adbik4/DL-FinalProject/Images/DL_PCB_preview1.png

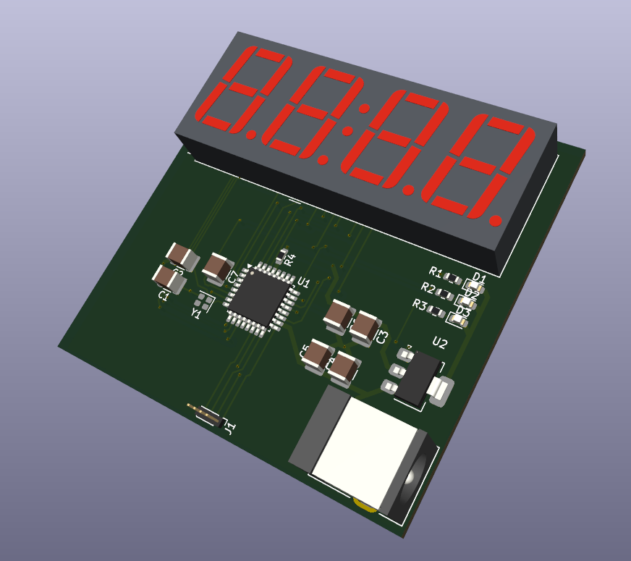
Images/DL_PCB_preview1.png
