adbik4/DL-FinalProject/Images/DL_PCB_state1.png

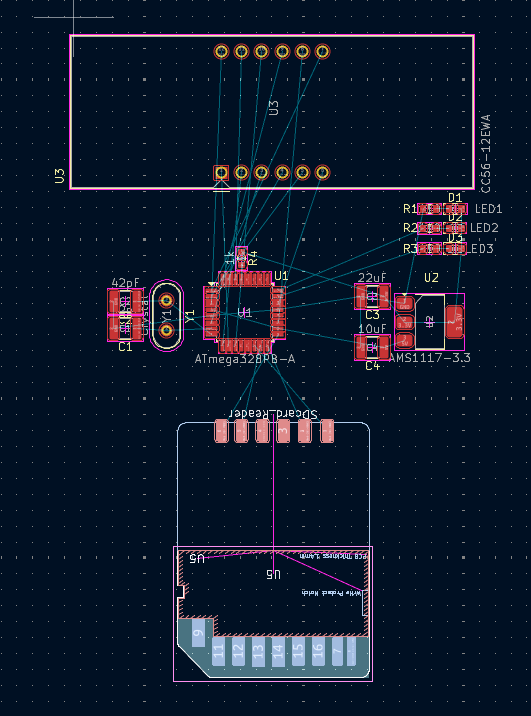
Images/DL_PCB_state1.png
