adbik4/DL-FinalProject/Images/DL_PCB_state3.png

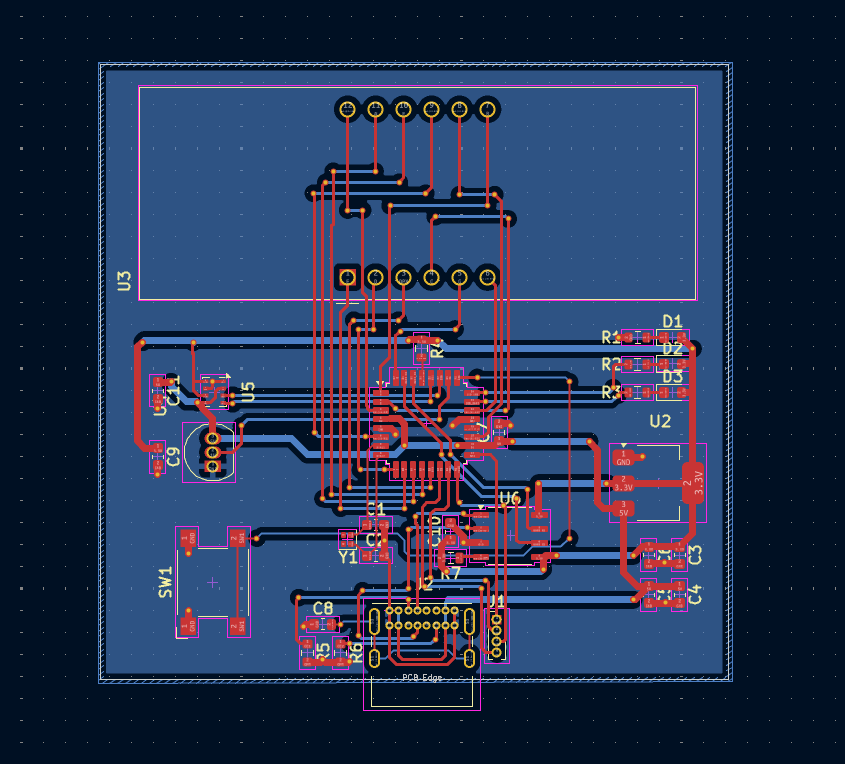
Images/DL_PCB_state3.png
