adbik4/DL-FinalProject/Images/DL_PCB_state4.png

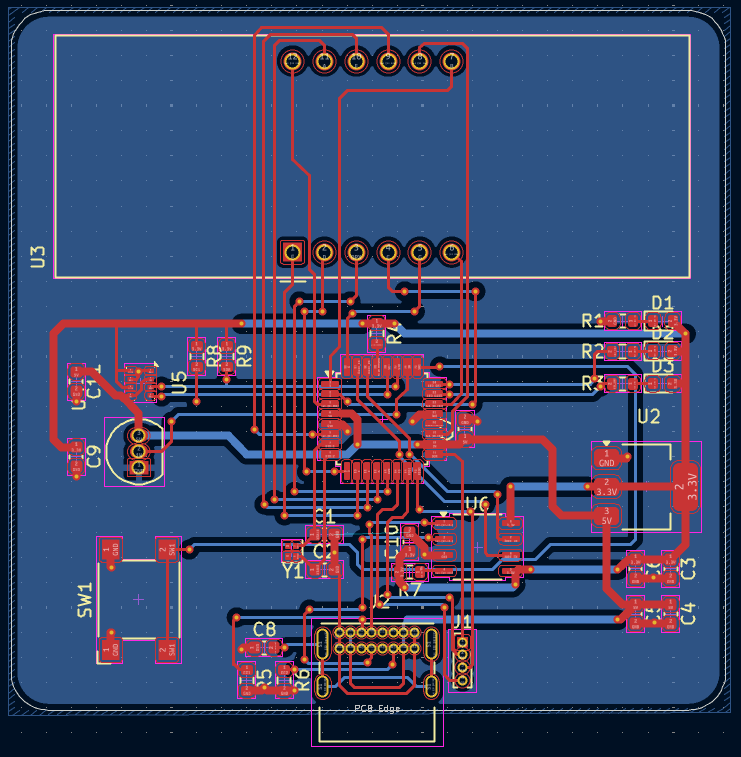
Images/DL_PCB_state4.png
