adbik4/DL-FinalProject/DL_Project/designlab_kopia_1/designlab_kopia_1/main.h

/*
 * main.h
 *
 * Created: 04/11/2025 15:06:42
 *  Author: Adrian
 */ 


#ifndef MAIN_H_
#define MAIN_H_

#define F_CPU 16000000UL 
#include <avr/io.h>
#include <util/delay.h>

#include <avr/interrupt.h>

#endif /* MAIN_H_ */
