adbik4/DL-FinalProject/DL_Project/designlab_kopia_1/designlab_kopia_1/display.h

/*
 * _7segm.h
 *
 * Created: 04.11.2025 15:49:14
 *  Author: artur
 */ 


#ifndef segmSEGM_H_
#define segmSEGM_H_

void SevenSeg_Init(void);
void SevenSeg_Update(void);
void SevenSeg_Show(int num);


#endif /* 7SEGM_H_ */
