adbik4/DL-FinalProject/DL_Project/designlab_kopia_1/designlab_kopia_1/diodes.h

/*
 * diodes.h
 *
 * Created: 04/11/2025 15:05:56
 *  Author: Adrian
 */ 


#ifndef DIODES_H_
#define DIODES_H_

void diode_pb0_on(void);
void diode_pb0_off(void);
void diode_pb1_on(void);
void diode_pb1_off(void);


#endif /* DIODES_H_ */
